paulgrammy/Student-Research-Project/doc/Circuit Frequency Response .png

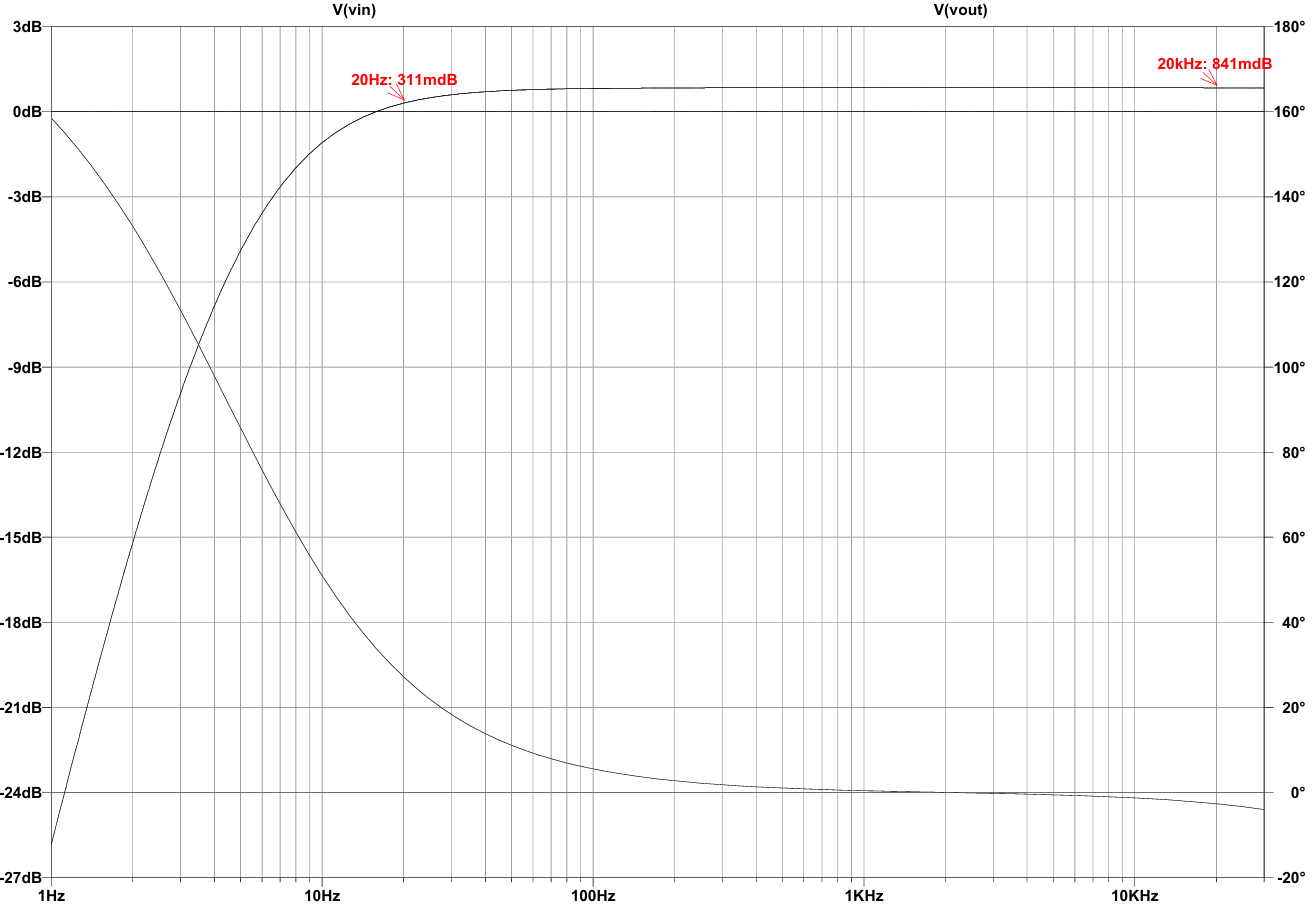
doc/Circuit Frequency Response .png
