paulgrammy/Student-Research-Project/doc/LTSpice Circuit.png

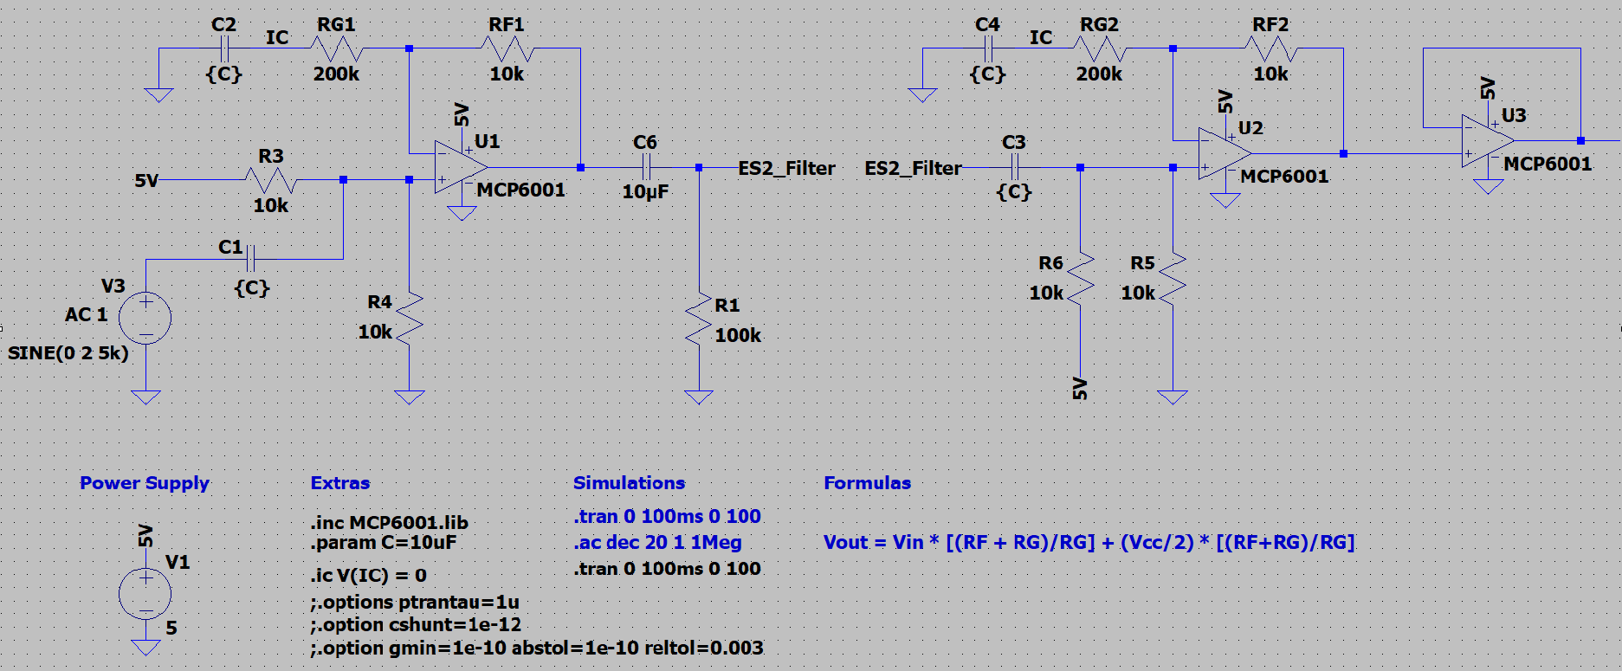
doc/LTSpice Circuit.png
