paulgrammy/Student-Research-Project/doc/PCB 3D View.png

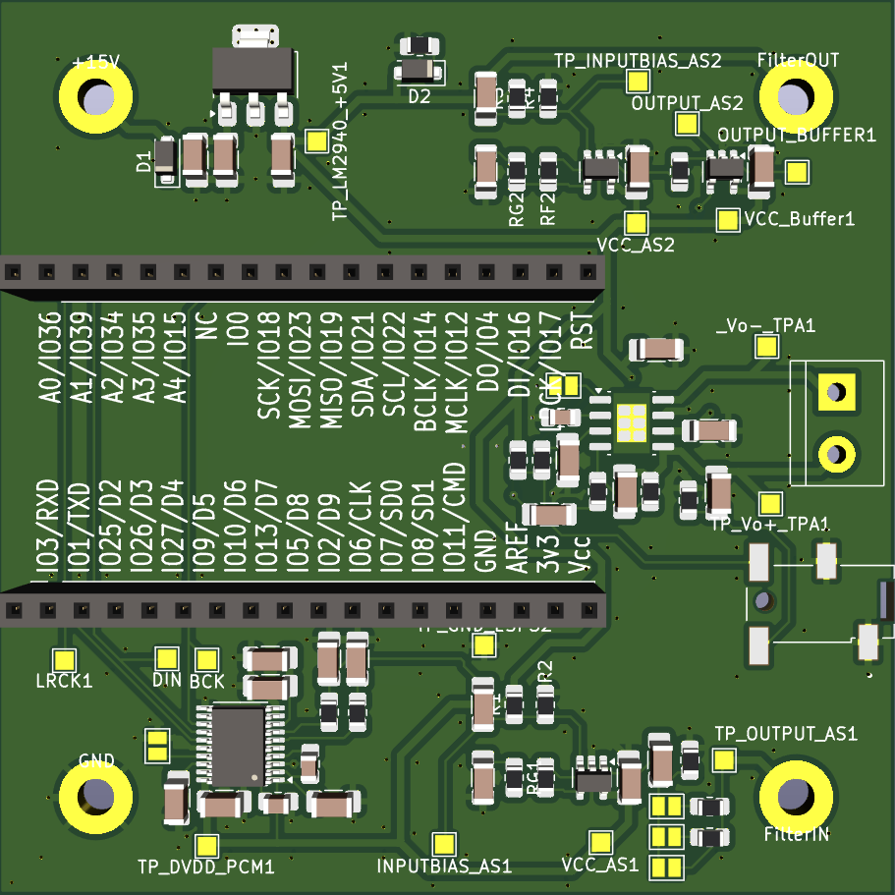
doc/PCB 3D View.png
