paulgrammy/Student-Research-Project/doc/PCB Layout.png

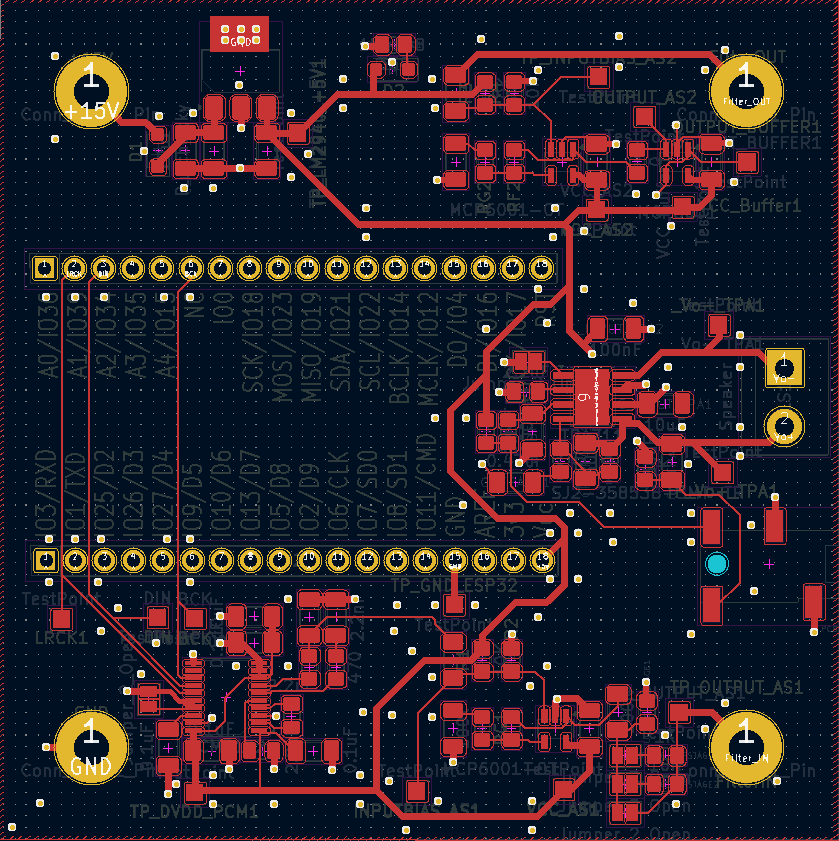
doc/PCB Layout.png
