paulgrammy/Student-Research-Project/doc/Schematic_OPAMP2.png

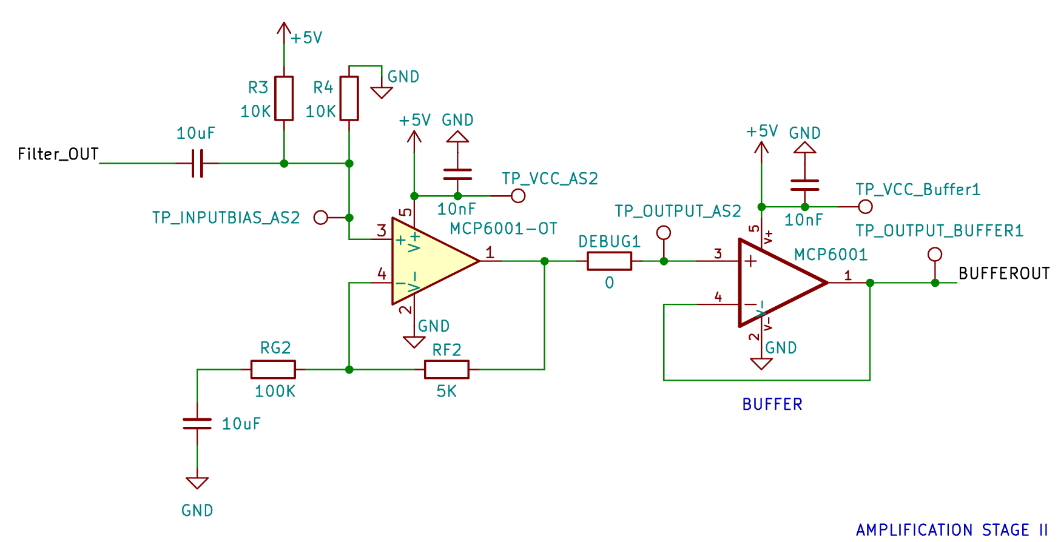
doc/Schematic_OPAMP2.png
