paulgrammy/Student-Research-Project/doc/TPA711 Typical application.png

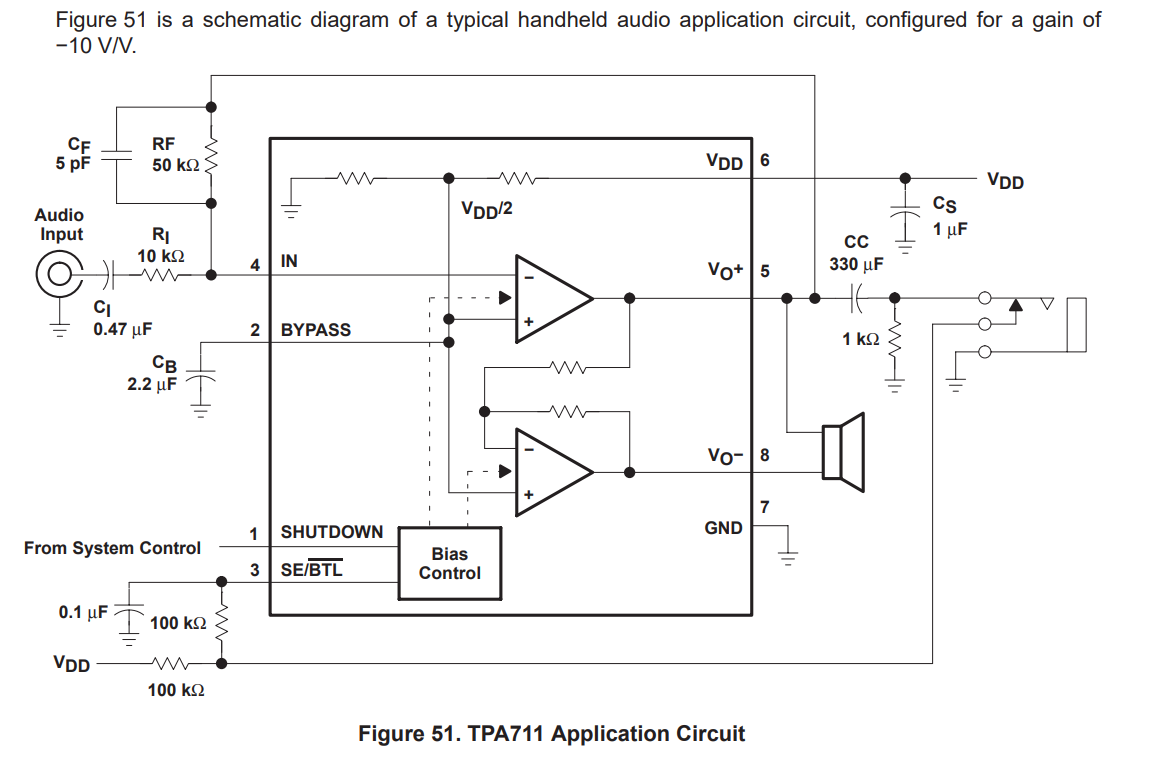
doc/TPA711 Typical application.png
