paulgrammy/Student-Research-Project/doc/Transient Response Zoomed.png

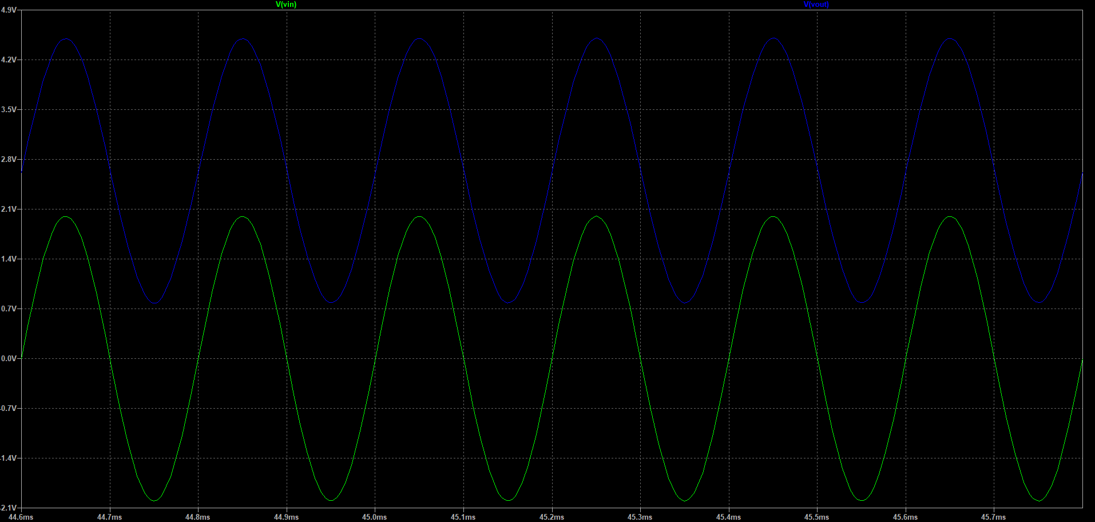
doc/Transient Response Zoomed.png
