paulgrammy/Student-Research-Project/doc/Transient Response.png

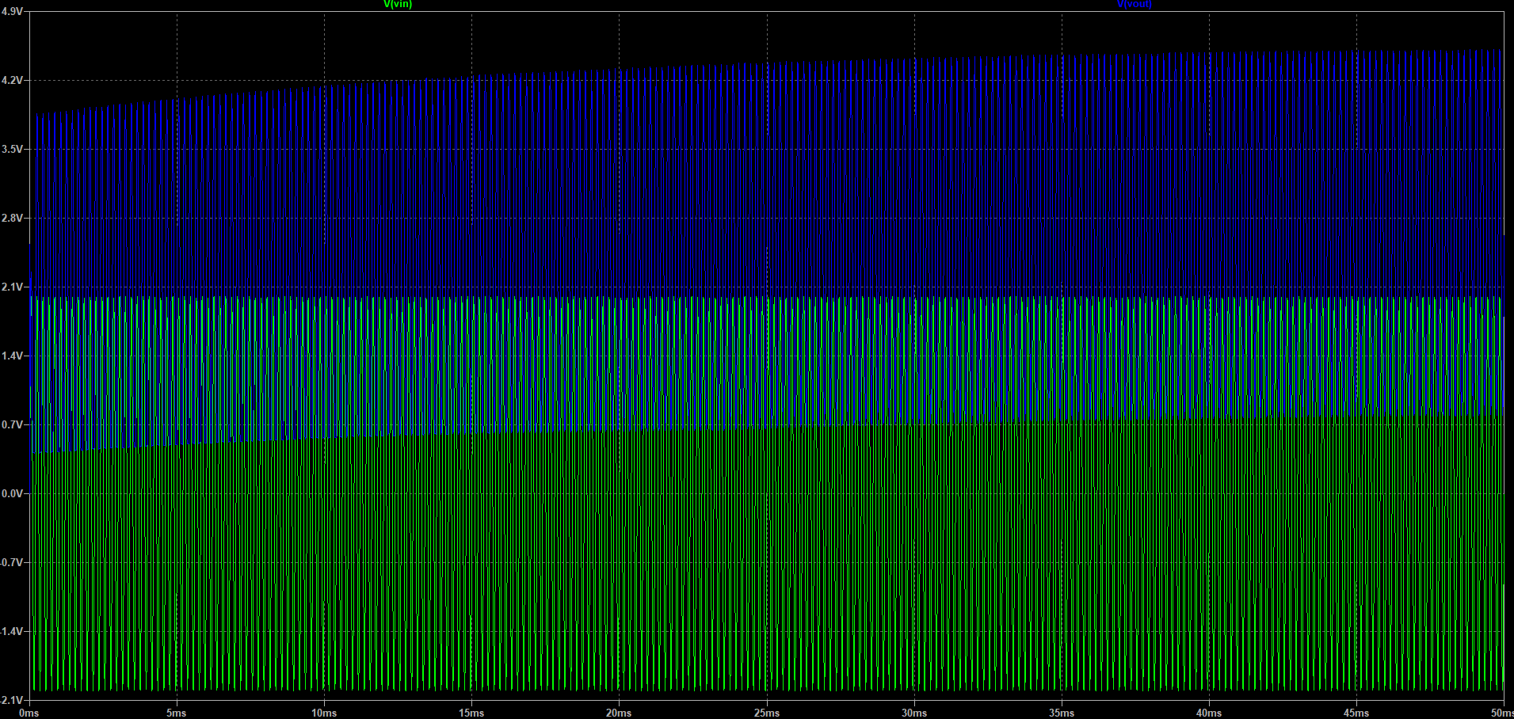
doc/Transient Response.png
