paulgrammy/Student-Research-Project/out/doc/BlockDiagram/BlockDiagram.png

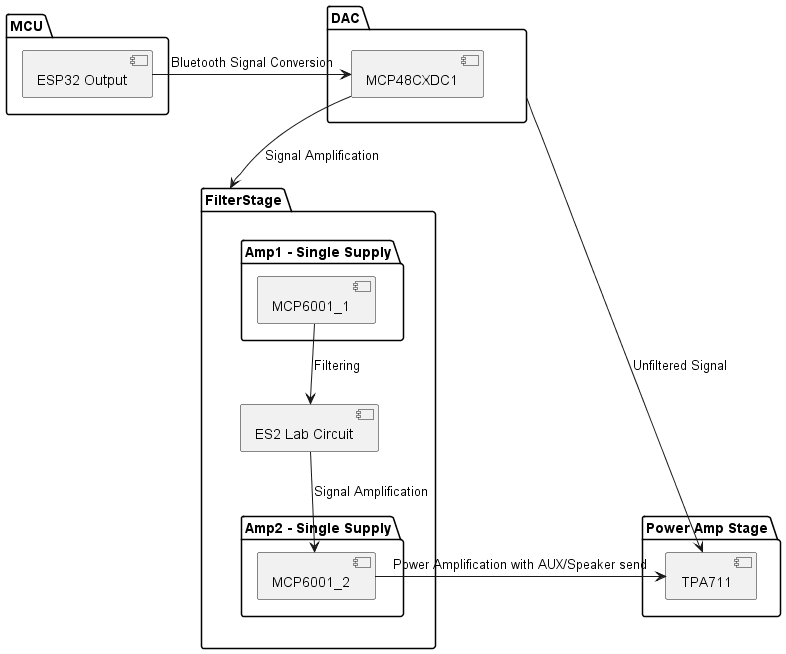
out/doc/BlockDiagram/BlockDiagram.png
